ccrawford/CC_KAP140_LCD/Photos/IMG_3196.JPEG

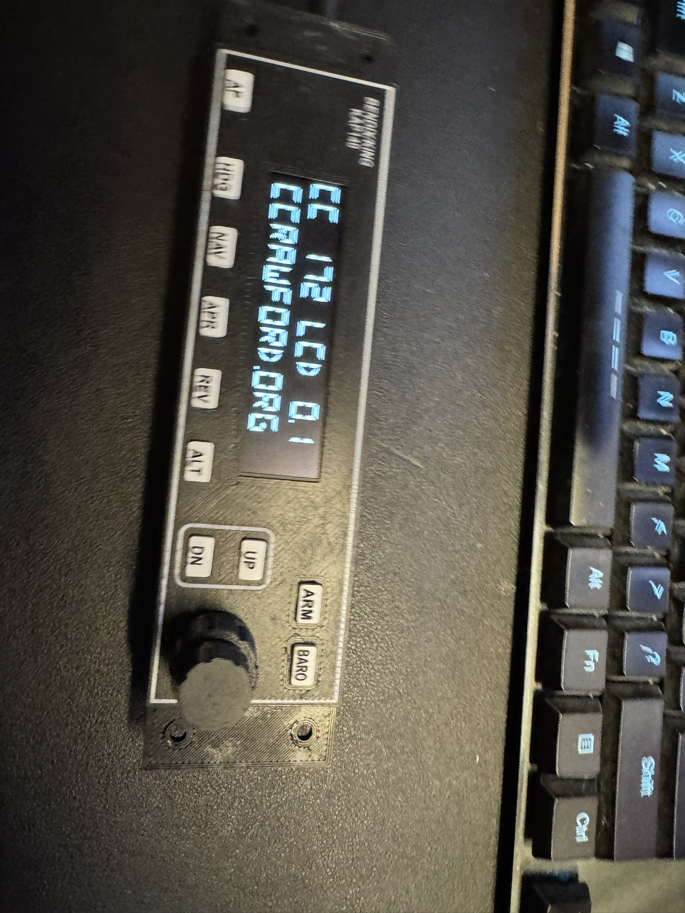
Photos/IMG_3196.JPEG
