ccrawford/CC_KAP140_LCD/Photos/IMG_3197.JPEG

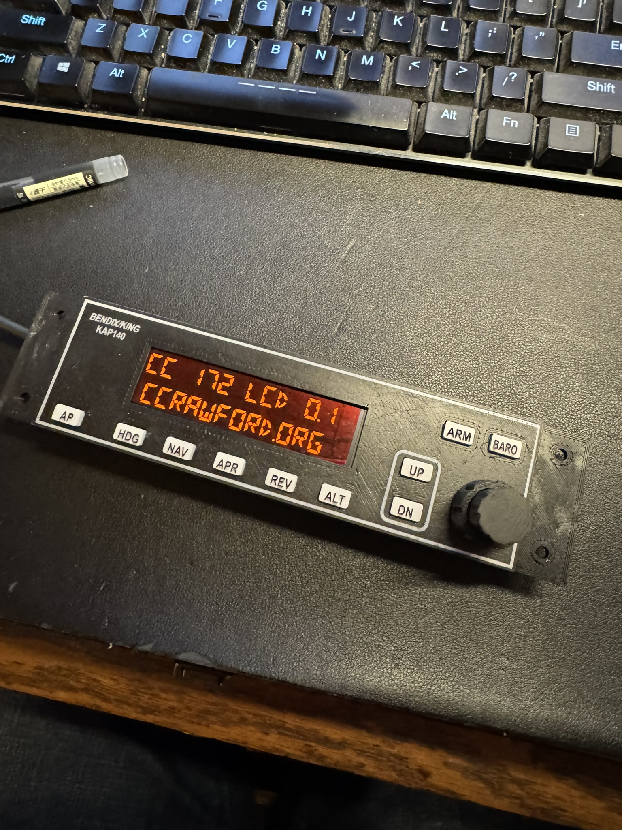
Photos/IMG_3197.JPEG
