ccrawford/CC_KAP140_LCD/Photos/IMG_3201.JPEG

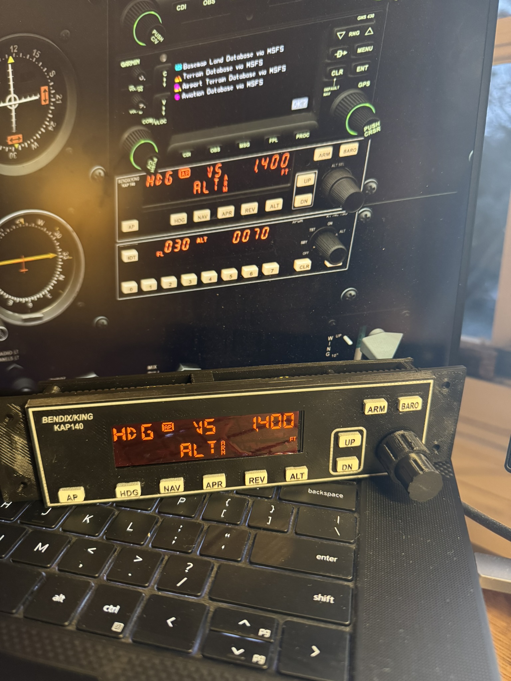
Photos/IMG_3201.JPEG
