ccrawford/CC_KAP140_LCD/Photos/IMG_3209.JPG

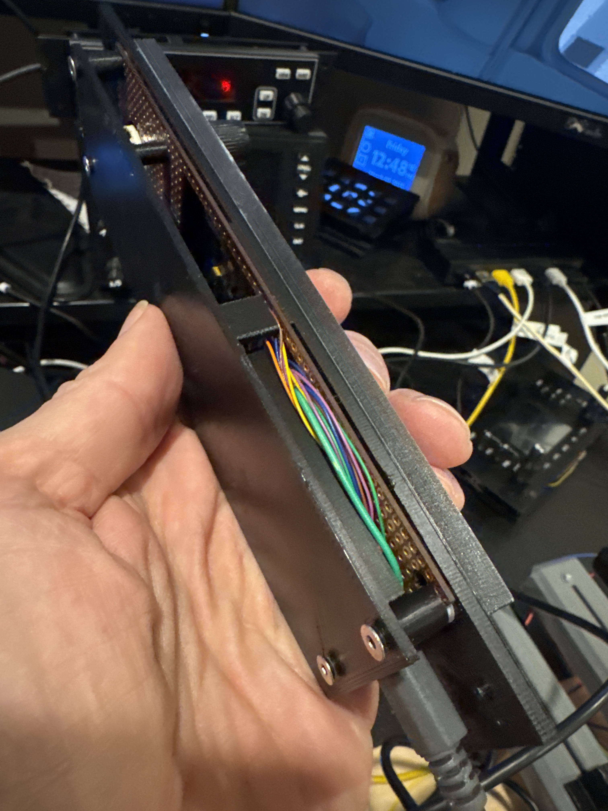
Photos/IMG_3209.JPG
