ccrawford/CC_KAP140_LCD/Photos/IMG_3215.JPEG

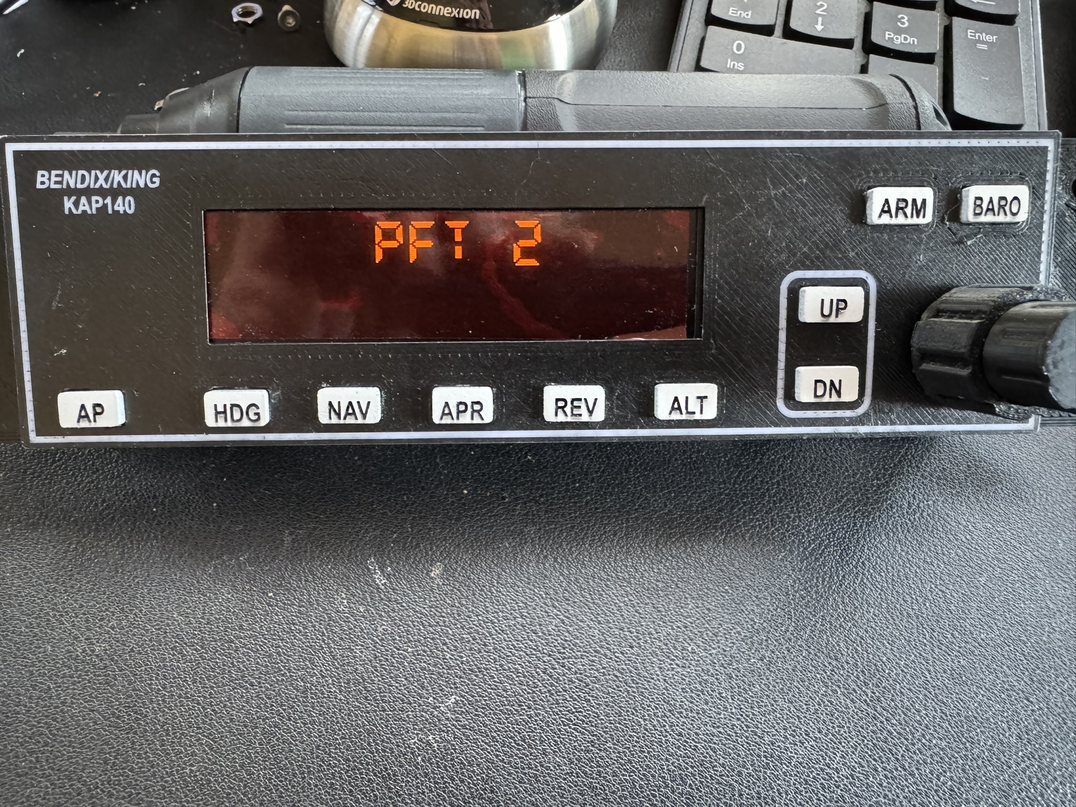
Photos/IMG_3215.JPEG
