ccrawford/CC_KAP140_LCD/Photos/IMG_3216.JPEG

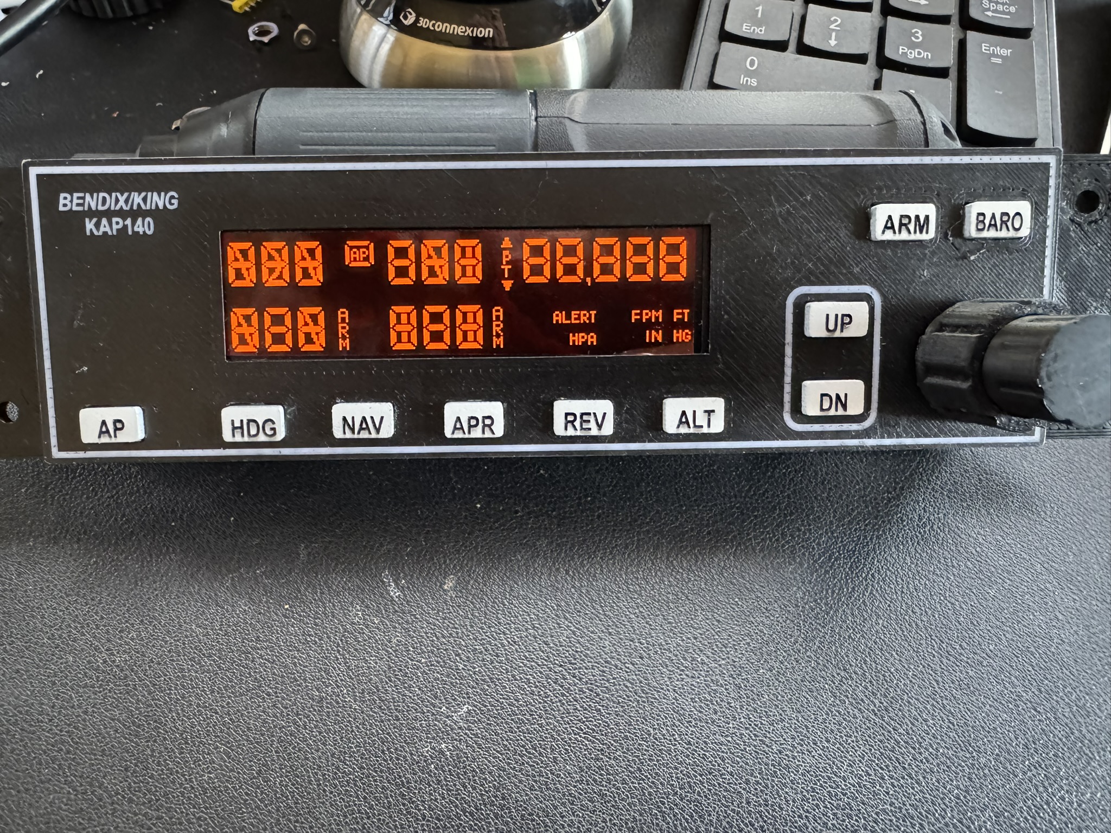
Photos/IMG_3216.JPEG
