ccrawford/CC_KAP140_LCD/CC_KAP140_LCD/kap140_20b_font.h

#pragma once
/*   Fontname: KAP 140 20p bold   Copyright: CCrawford 2025   Glyphs: 96/96   BBX Build Mode: 0 */ const uint8_t KAP_140_20b_font[2014] U8G2_FONT_SECTION("KAP_140_20b_font") =    "`\0\4\4\5\5\5\6\6\30\31\0\376\27\14\6\0\2\370\6\307\7\301 \6\0@\20\6!\42\316"   "\350\60\207 !\306\210\10\22\42H\210 %\202\204\10\42$\304\220\42!\2\5\21\22\42P\220\0\42"   "\23\310\304V\5\22\244B\204\12A$D\250\20\241B\0#*\327\304\66\17!\201H\14!\22\42P"   "$Q\4\11\21hH,H\4\12\64&D\220\20\201\242\10\23\42H\10*\202D\1\0$\37\317H"   "\60\226\60aJD\22*H\230\20\241\202\224\10\25$L\210PA\302\204 \22\4\0%\27\206F\20"   "\25Ab\210\220\60=&HL\306\204\12Z&T\334\0&\30\206F\20\215\61Ab\62&T\320\62"   "\241\342\36\200\11\42d\4\11\1'\32\313X\60\216!a\304\204\20\42&D\24bB\4\31\23\42L"   "\210!a\2(\23\311Dp\5\22a\2\205\31\22&P\230@a\2\21) \321@\60\216!D\302"   "\210\11\21&H\210 b\10\205\12\22&\222\60!\302D\63\204P\20\0*\15\304D\320\204\21A\204"   "\220\210I\0+\6\0@\20\6,\10\202@O\4\22\21-\12jPU\16\24*P\0.\7B@"   "P\4\2/\10\1I\266\4\23\1\60\36\356JP\16\66J\202 \31Z\320\16\213\16\16\36xhA"   ";,:\4I\20\65,\0\61\21cvQ\226\20\17D\10\11\25\342\201\10!\1\62\36\356JP\16"   "\66\252\220\4\26;\217\305 \11\242$\10\32\301c\347Vp\20TjX\0\63\35\355NP\6&\212"   "\220\204\25:o\205 \11\241\10IX\241\363V\10\222\20JX\0\64\30nJQ\206\300C\13\332a"   "\321!H\202\250B\22X\354<\26\35\0\65\36\356JP\16\66J\202\240\21<vn\5\7A\245\12"   "I`\261\363X\14\222 jX\0\66 \356JP\16\66J\202\240\21<vn\5\7A\245$\10\222"   "\241\5\355\260\350\20$A\324\2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
