ccrawford/CC_KAP140_LCD/CC_KAP140_LCD/kap140b_font.h

/*
  Fontname: KAP140
  Copyright: Copyright (c) 2025, Chris Crawford
  Glyphs: 128/256
  BBX Build Mode: 0
*/
const uint8_t kap140b_font[1989] U8G2_FONT_SECTION("kap140b_font") = 
  "\200\0\4\3\4\5\5\5\5\16\30\0\373\20\373\21\375\3\33\5\257\7\250\0\6\0 \214\0\1\6\0"
  " \214\0\2\6\0 \214\0\3\6\0 \214\0\4\6\0 \214\0\5\6\0 \214\0\6\6\0 \214"
  "\0\7\6\0 \214\0\10\6\0 \214\0\11\6\0 \214\0\12\6\0 \214\0\13\6\0 \214\0\14"
  "\6\0 \214\0\15\6\0 \214\0\16\6\0 \214\0\17\6\0 \214\0\20\6\0 \214\0\21\6\0"
  " \214\0\22\6\0 \214\0\23\6\0 \214\0\24\6\0 \214\0\25\6\0 \214\0\26\6\0 \214"
  "\0\27\6\0 \214\0\30\6\0 \214\0\31\6\0 \214\0\32\6\0 \214\0\33\6\0 \214\0\34"
  "\6\0 \214\0\35\6\0 \214\0\36\6\0 \214\0\37\6\0 \214\0 \6\0 \344\0!\24["
  " \344\20\21!\23\221\27\24\42\24i\42$\322D\4\42\17W \344\60A\24!\23\21\24\21\24\1"
  "#\23[ \344\21\22C\221&d\42F\42\233\220\210\210\5$':\243\343$(v\20\241HDH"
  "DHDHDJB\314LBJDHDHDHDHB\342 LP\10\0%\24\25#\274\22"
  "\63\62Q;\22\21\62\22\24\71\23\224\11\0&\24\25!\254\61\22\21\62\22\24\71\23\224q\305\310L"
  "\10\0'\21W \344 B\21\22!\23\221$\42I\4\0(\21Hg\343\65$\245\231\224\230~'"
  "&\247\335\0)\21Hc\343\60\247\63\71\61\375JLJ\243)\0*\27\11#\344q\21Q\61\305\325"
  "\134\304ED\305\24\257&*\42.\0+\15w\344\344\23\226fb&,\15\0,\10B\240\253P\21"
  "\1-\10'\344\345pQ\1.\6\42\42\344@/\27\11#\344q\21Q\61\305\325\134\304\212\10\25S"
  "\274\232\250\210\270\0\60\25\11#\344q\21Q\61\305\325\134d\334\24\257&*\42.\0\61\13\342p\344"
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
  "\77\223\220\22\71\10\324N\342 \4\0z\14\272\42\344p\60(\247\77<\30{\24] \354\60\61\21"
  "#\23\21!Q\61\221B&\215L\6|\10\42\253\343\360\7\1}\23i%\343@\250N\37\12\216M"
  "\211\311\351\63!*\0~\20V \344\20\21\42\241\42b\42D\42$\0\177\6\0 \344\0\0\0\0"
  "\4\377\377\0";
