ccrawford/CC_KAP140_LCD/CC_KAP140_LCD/MFCustomDevice.h

#pragma once

#include <Arduino.h>
#include "CC_KAP140_LCD.h"
#include "CC_KT76C_LCD.h"

// only one entry required if you have only one custom device
enum
{
    MY_AP_DEVICE = 1,
    MY_XPDR_DEVICE
};
class MFCustomDevice
{
public:
    MFCustomDevice();
    void attach(uint16_t adrPin, uint16_t adrType, uint16_t adrConfig, bool configFromFlash = false);
    void detach();
    void update();
    void set(int16_t messageID, char *setPoint);

private:
    bool getStringFromMem(uint16_t addreeprom, char *buffer, bool configFromFlash);
    bool _initialized = false;
    CC_KAP140_LCD *_myApDevice;
    CC_KT76C_LCD *_myXpdrDevice;
    uint8_t _pin1, _pin2, _pin3;
    uint8_t _customType = 0;
};
