ccrawford/CC_KAP140_LCD/CC_KAP140_LCD/kap140_20b_font_constants.h

// These should really be in the font file, but it auto-authors.
#define CHAR_WIDTH 18

#define GLYPH_AP 0x5B      // [
#define GLYPH_FT 0x22      // "
#define GLYPH_PITCHUP 0x25 // %
#define GLYPH_PITCHDN 0x26 // &
#define GLYPH_ARM 0x5D     // ]
#define GLYPH_ALERT 0x23   // #
#define GLYPH_IN 0x7E      // ~
#define GLYPH_HG 0x5E      // ^
#define GLYPH_HPA 0x21     // !
#define GLYPH_FPM 0x7B     // {
#define GLYPH_FL 0x28      // (
#define GLYPH_R 0x2A       // *
#define GLYPH_ALT 0x24     // $
#define GLYPH_ON 0x27      // '
#define GLYPH_GND 0x3D     // =
#define GLYPH_SBY 0x29     // )
#define GLYPH_INDICATOR 0x3F  // ? (This is an up pointing triangle)
